Ryzee119/XboxHDMI-Ryzee119/src/adv7511.h

// Copyright 2021, Ryan Wendland, XboxHDMI by Ryzee119
// SPDX-License-Identifier: MIT

#ifndef ADV7511_H_
#define ADV7511_H_

#include <stdbool.h>
#include "stm32f0xx_hal.h"

#define BIT(nr) (1UL << (nr))

#define ADV7511_INT0_HPD BIT(7)
#define ADV7511_INT0_MONITOR_SENSE BIT(6)

#define ADV7511_VIC_CHANGED 0x80
#define ADV7511_VIC_CHANGED_CLEAR 0x7F
#define ADV7511_VIC_UNAVAILABLE 0
#define ADV7511_VIC_VGA_640x480_4_3 1
#define ADV7511_VIC_480p_4_3 2
#define ADV7511_VIC_480p_16_9 3
#define ADV7511_VIC_720p_60_16_9 4
#define ADV7511_VIC_1080i_60_16_9 5

/* Hardware defined default addresses for I2C register maps */
#define ADV7511_MAIN_I2C_ADDR 0x72           //0x72>>1
#define ADV7511_CEC_I2C_ADDR_DEFAULT 0x78    //0x78>>1
#define ADV7511_EDID_I2C_ADDR_DEFAULT 0x7E   //0x7E>>1
#define ADV7511_PACKET_I2C_ADDR_DEFAULT 0x70 //0x70>>1

static const uint8_t identityMatrix[] = {
    0xA8, 0x00, 0x00, 0x00, 0x00, 0x00, 0x00, 0x00,
    0x00, 0x00, 0x08, 0x00, 0x00, 0x00, 0x00, 0x00,
    0x00, 0x00, 0x00, 0x00, 0x08, 0x00, 0x00, 0x00};

static const uint8_t CscYcc709ToRgb[] = {
    0xAC, 0x51, 0x08, 0x00, 0x00, 0x00, 0x19, 0xD7,
    0x1C, 0x54, 0x08, 0x00, 0x1E, 0x89, 0x02, 0x91,
    0x00, 0x00, 0x08, 0x00, 0x0E, 0x87, 0x18, 0xBC};

static const uint8_t CscYuv709ToRgb[] = {
    0xE7, 0x2C, 0x04, 0xA7, 0x00, 0x00, 0x1C, 0x1F,
    0x1D, 0xDD, 0x04, 0xA7, 0x1F, 0x26, 0x01, 0x34,
    0x00, 0x00, 0x04, 0xA7, 0x08, 0x75, 0x1B, 0x7A};

static const uint8_t CscYcc601ToRgb[] = {
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
    0x00, 0xCB, 0x00, 0x00, 0x07, 0x21, 0x00, 0x09};

static const uint8_t CscYcc601LRtoYcc709LR[] = {
    0xA8, 0x33, 0x00, 0x00, 0x00, 0x99, 0x1F, 0x99,
    0x1E, 0x56, 0x08, 0x00, 0x1F, 0x13, 0x01, 0x4B,
    0x00, 0xEA, 0x00, 0x00, 0x08, 0x26, 0x1F, 0x78};

static const uint8_t CscYcc601LRtoYcc601FR[] = {
    0xA9, 0x1B, 0x00, 0x00, 0x00, 0x00, 0x1F, 0x6E,
    0x00, 0x00, 0x09, 0x50, 0x00, 0x00, 0x1F, 0x6B,
    0x00, 0x00, 0x00, 0x00, 0x09, 0x1B, 0x1F, 0x6E};

static const uint8_t CscYcc601FRtoYcc601LR[] = {
    0x8E, 0x0D, 0x00, 0x00, 0x00, 0x00, 0x01, 0x00,
    0x00, 0x00, 0x0D, 0xBC, 0x00, 0x00, 0x01, 0x00,
    0x00, 0x00, 0x00, 0x00, 0x0E, 0x0D, 0x01, 0x00};

static const uint8_t CscYcc601LRtoYcc709FR[] = {
    0xA9, 0x56, 0x00, 0x00, 0x00, 0xAE, 0x1E, 0xFE,
    0x1E, 0x0E, 0x09, 0x5A, 0x1E, 0xEC, 0x00, 0xED,
    0x01, 0x0B, 0x00, 0x00, 0x09, 0x46, 0x1E, 0xD7};

enum adv7511_sync_polarity
{
    ADV7511_SYNC_POLARITY_PASSTHROUGH,
    ADV7511_SYNC_POLARITY_LOW,
    ADV7511_SYNC_POLARITY_HIGH,
};

typedef struct
{
    uint8_t hot_plug_detect;
    uint8_t monitor_sense;
    uint8_t interrupt;
} adv7511;

uint8_t adv7511_power_up(I2C_HandleTypeDef *i2c, adv7511 *encoder);
uint8_t adv7511_update_register(I2C_HandleTypeDef *i2c, uint8_t address, uint8_t mask, uint8_t new_value);
uint8_t adv7511_read_register(I2C_HandleTypeDef *i2c, uint8_t address);
uint8_t adv7511_write_register(I2C_HandleTypeDef *i2c, uint8_t address, uint8_t value);
uint8_t adv7511_write_cec(I2C_HandleTypeDef *i2c, uint8_t address, uint8_t value);
void adv7511_struct_init(adv7511 *encoder);
uint8_t apply_csc(I2C_HandleTypeDef *i2c, uint8_t *coefficients);

#endif /* ADV7511_H_ */
